Murphyramiritus/planta-nivel-umsa---Public/historico/2022-II/lista de pendientes.docx

VIDEOS:

Isabel: Sensor de temperatura RTD TST487

Sensor de temperatura TC12

Configurar el controlador de temperatura para visualizar los sensores TC y RTD (por realizar)

Configuración PID para el controlador de temperatura (por realizar)

Guido: Manejo del dosificador

Carpeta (Dosificador)

Dosificador Burkert 8035 (por realizar)

Modelo control de temperatura (por realizar)

Roger: SensorUltrasonicoAllenBradley

PrincipioDeFuncionamiento-SensorUltrasonico

Sensor ultrasónico- Allen Bradley modelo 873P-DCAC1S-D5: Características generales – programación – pruebas de laboratorio

Explicación del bloque PID – enfoque continuo (realizado)

Explicación del bloque PID – enfoque Discreto (realizado)

https://drive.google.com/file/d/1aOzCxuXivyHkaeiTq-OtF0UfNlqLcX1q/view?usp=share_link

Controlador PI para el sistema de nivel de líquido (realizado)

https://drive.google.com/file/d/1sBpz8i9ndp3X9Kgfs4qF4b5X31JhYju9/view?usp=share_link

Milton: Motor Bomba y electroválvulas

Funcionamiento del Sistema

Control aplicado al sistema (Por Realizar)

Alvaro: Sensor de presión

Energización (Editar)

Variador de frecuencia (Editar)

Instalación de la máquina virtual (por realizar)

Inducción para el uso de Rslogix y su vinculación al PLC (por realizar)

Diego: Sensor Vibratorio Funcionamiento

Lab_SensVibratorio
