Murphyramiritus/planta-nivel-umsa---Public/historico/2022-II/902/Bitácoras/Bitacora Lab 4_ETN902.docx

Universidad “Mayor de San Andrés”

FACULTAD DE INGENIERIA


CONTROLADOR DEL SISTEMA DE NIVEL DE LIQUIDO

Integrantes: Univ. Espino Marca Mary Isabel

Univ. Condori Mamani Roger

Univ. Linares Poma Guido Alvaro

Carrera: Ing. Electrónica

Materia: ETN 902 / ETN 1034

Docente: Ing. Jorge A. Nava A.

Auxiliares: Univ. Huarachi M. Rhem J.

Univ. Huanca Mita Miguel

Fecha: 13/12/2022

La Paz – Bolivia

Linealización

Se tiene un tanque vertical abierto, provisto de un orificio o restriccion de descarga en su parte inferior, el tanque tiene un area A=l_1 xl_2 , tiene un caudal de entrada q_e por la parte superior , y un caudal q_s a la atmosfera por el orificion mencionado anteriormente.

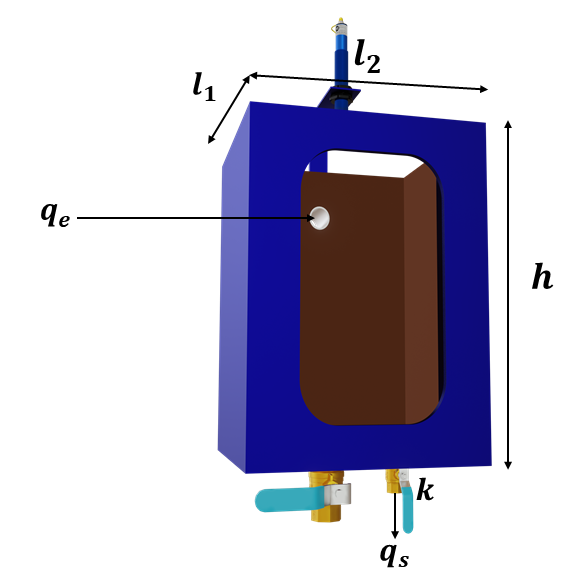
[picture p266: figure]

El caudal que fluye por una una restriccion sigue, basicamente, una ley cuadratica con la presion diferencial, pues se asume regimen turbulento.

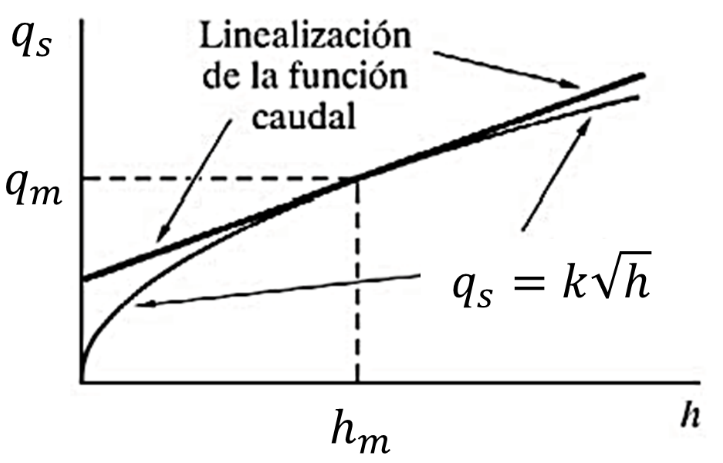
[picture p267: figure]

En nuestro caso , un tanque abierto a la atmosfera, la presion diferencial en la restriccion de salida es debida a la presion hidrostatica existente como consecuencia del nivel de liquido en el tanque.

Si h es la altura del liquido, y k es un coeficiente dependiente de la geometria de la restriccion y de la densidad del liquido, el caudal de salida sera.

q_s =k√h (1)

Balance masico de caudales

entrada-salida=acumulacion

Por otra parte (dV)/(dt) es un caudal, y por otra parte dV=Adh , se tendria:

q_e -q_s =A(dh)/(dt) (2)

Es intuitivo el hecho de que, para un caudal de entrada constante, el nivel se estabilizara en un punto determinado, cuando la salida se iguale con la entrada, ya que a mayor nivel, mayor caudal de salida y viceversa.

Remplazando (2) en (1)

q_e -k√h=A(dh)/(dt) (3)

La ecuacion (3) es una funcion no lineal, entonces para linealizar se escoge un punto de equilibrio, es decir halla la altura de equilibrio h_0 , dado un determinado caudal de entrada q_e .

Entonces q_e =q_s y por tanto h=((q_s)/k)^2 . Pero el calculo se complica para condiciones transitorias , cuando q_s ≠q_e .

Es por ello, que en estos casos se procede linealizar la funcion de la ecuacion (3), mediante alguna forma de ecuacion aproximada, de tal manera que la ecuacion del caudal de salida q_s es sustituida por una ecuacion lineal.

Para ello se define una valor medio de h_m , preferentemente al nivel normal de trabajo, al que llamaremos nivel medio h_m y se opera con una funcion que corresponda a la ecuacion de una recta tangente a la funcion original en el punto [ h=h_m , q_s =q_m ].

Los valores medios, para el nivel medio normalmente el nivel de trabajo seran:

- Pendiente m de la recta tangente

m=(dq_s)/(dh)|_(h=h_m) =1/2k1/(√(h_m)) (4)

- Caudal medio de salida q_m :

q_m =k √(h_m) (5)

Por lo que:

k=(q_m)/(√(h_m)) (6) y, m=(q_m)/(2h_m) (7)

Efectuando un cambio de cordenadas a [ h_m , q_m ], en donde q y h representan los valores absolutos de las variables.

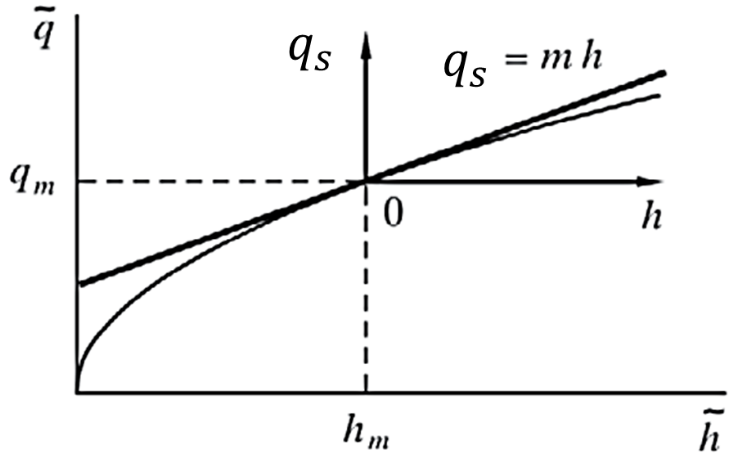
[picture p268: figure]

Con lo que la nueva ecuacion del balance masico queda:

q_e -mh=A(dh)/(dt) (8)

Reordenando y aplicando la transformada de laplace a la ecuacion (8)

Q_e =AsH+mH=H(As+m)

Entonces la función de transferencia será:

H/(Q_e)=1/(As+m)=(1/m)/((As)/m+1)=K/(Ts+1)

H/(Q_e)=K/(Ts+1) (9) funcion de transferencia linealizada

Donde:

K=1/m=Ganancia del sistema

T=A/m=Constante de tiempo

En el laboratorio se obtuvo las siguientes mediciones:

h_m =0.367m

q_m =0.28x10^(-3) (m^3)/s

Realizando calculos y remplazando en (9)

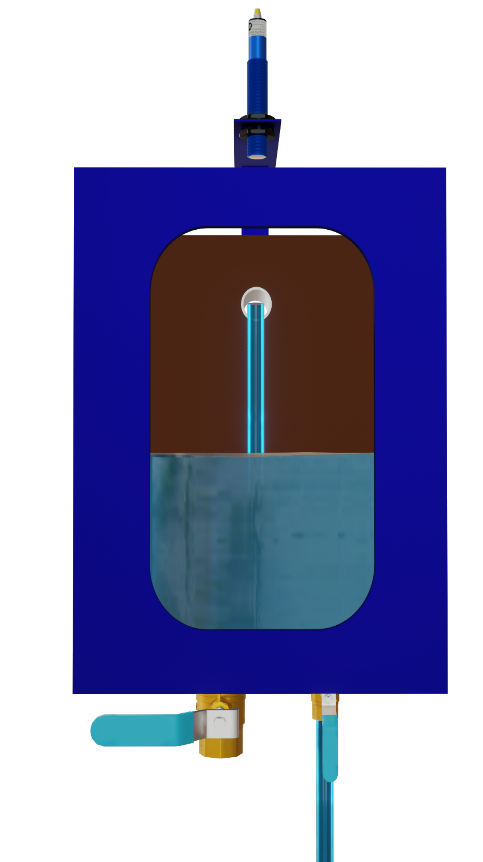
[picture p269: figure]

m=(q_m)/(2h_m)=(0.28x10^(-3))/(2⋅0.367)=0.381x10^(-3) (m^2)/s

H/(Q_e)=1/(As+m)=(1/m)/((As)/m+1)=2624.67/(419.95s+1)

H/(Q_e)=2624.67/(419.95s+1) funcion de transferencia analitica

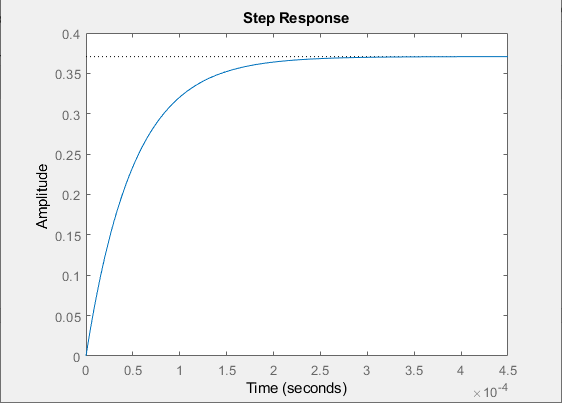
[picture p270: figure]

Por otro lado realizando la linealizacion por series de taylor, tomando la siguiente ecuación no lineal:

A(dh)/(dT)=qe-k_2 a√(2gh)

Realizando la linealizacion se obtiene:

H/(Q_e)=1/(A S+(K_2 a √5)/(√(h_0)))

H/(Q_e)=1/(0.16 S+(0.02√5)/(√0.187))

H/(Q_e)=1/(0.16 S+(0.02√5)/(√0.187))

H/(Q_e)=1/(0.16 S+0.103)

Donde:

A=Area en m^2

h_0 =Altura donde el caudal de salida y entrada es igual,es decir no hay cambio en la altura

a=Areade la valvula de salida (del pequeño)

K_2 =Llave de paso que varia entre 0 y 1, tomando como 1 totalmente abierta

H=Altura de nivel

Q_e =Entrada de caudal

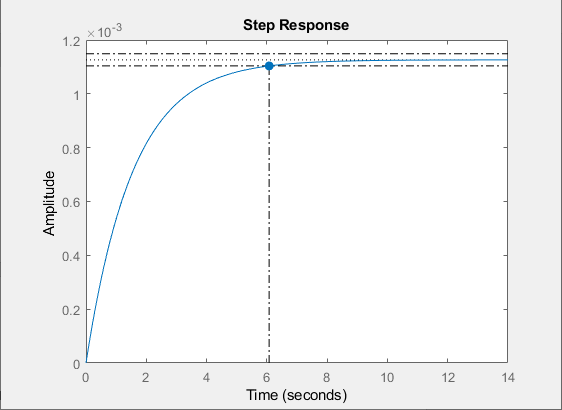
[picture p271: figure]

MODELO DE LA PLANTA

Se tiene un tanque vertical abierto, provisto de un orificio o restricción de descarga en su parte inferior, el tanque tiene un área A=l_1 xl_2 , tiene un caudal de entrada q_e por la parte superior , y un caudal q_s a la atmosfera por el orificio mencionado anteriormente.

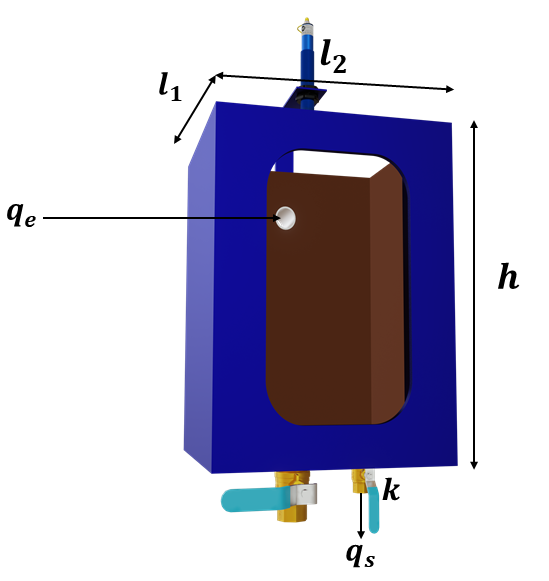
[picture p272: figure]

Donde:

A=l_1 xl_2 : área del tanque

q_e : caudal de entrada

q_s : caudal de salida

k: coeficiente de restricción

h: altura del deposito

Ecuaciones fundamentales

Aplicando la transformada de Laplace

Caudal por la restricción

Caudal en la capacidad del tanque

Reordenando y reemplazando la ecuación (6) y (8) en (3)

Despejando obtenemos la función de transferencia

En el laboratorio se obtuvo las siguientes medidas:

Realizando cálculos y remplazando

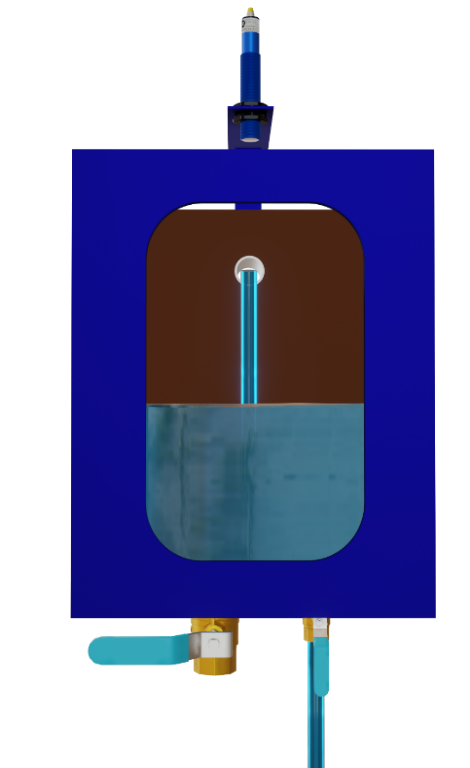
[picture p273: figure]

Vista frontal del tanque superior

Función de transferencia experimental

La FT experimental se obtuvo tomando datos de la altura h cada 20 (s) hasta que logre alcanzar su punto de equilibrio con un caudal de entrada

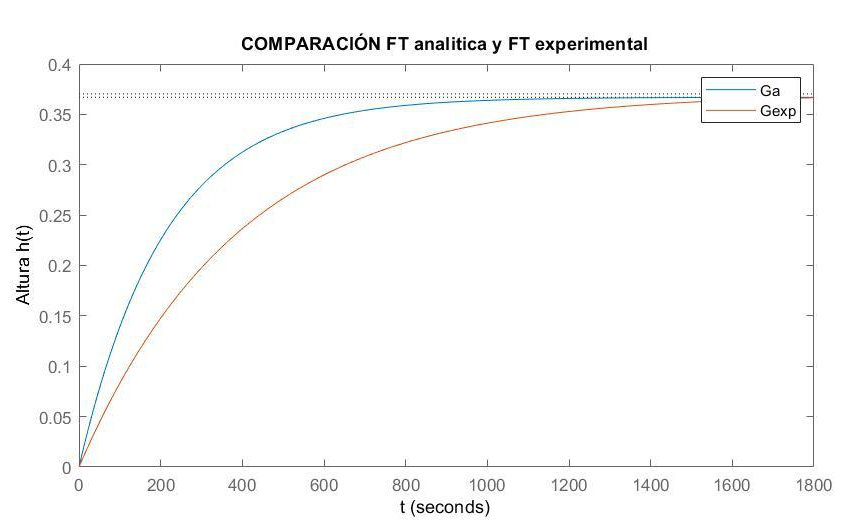
[picture p274: figure]

DIAGRAMA EN BLOQUES

h(t)

h(t)

qe(t)

u(t)

e(t)

ref

CONTROL

ACTUADOR

PLANTA

SENSOR

PID

h(t)

h(t)

qe(t)

u(t)

e(t)

ref

CONTROL

VDF +Bomba

PLANTA

SENSOR

+

- G_(VDF) es la función de transferencia del variador de frecuencia más la bomba

G_(VDF) =(Q_(max))/f

- G_s es la función de transferencia del sensor

G_s =1

Porque la altura que va tomar en el tanque la va a enviar tal cual al comparador

- G_P es la función de transferencia de la planta

H/(Q_e)=1/(0.16 S+0.103)

Elementos a utilizar

- PLC Micro Logix 1100 (Controlador)
- Sensor ultrasónico (sensor en la realimentación)
- Sensor de presión (sensor en la realimentación, opcional)
- Sensores vibratorios (para marcar las limitaciones del tanque)
- Variador de frecuencia y bomba (actuador)

Instrumentos de Medición

- Flujómetro (para medir el caudal de entrada)

Definición de variables

Válvula pequeña siempre abierta (parte del sistema)

Válvula grande como perturbación.

Variable a controlar: El caudal de entrada

Variable Medible: Corriente en función de altura (sensor ultrasónico) que se entrega al PLC

Variable Controlada: Altura del nivel de líquido

Variable manipulada: Frecuencia del VFD

Perturbación: Caudal de Salida válvula grande, agregación de líquido en el tanque superior.

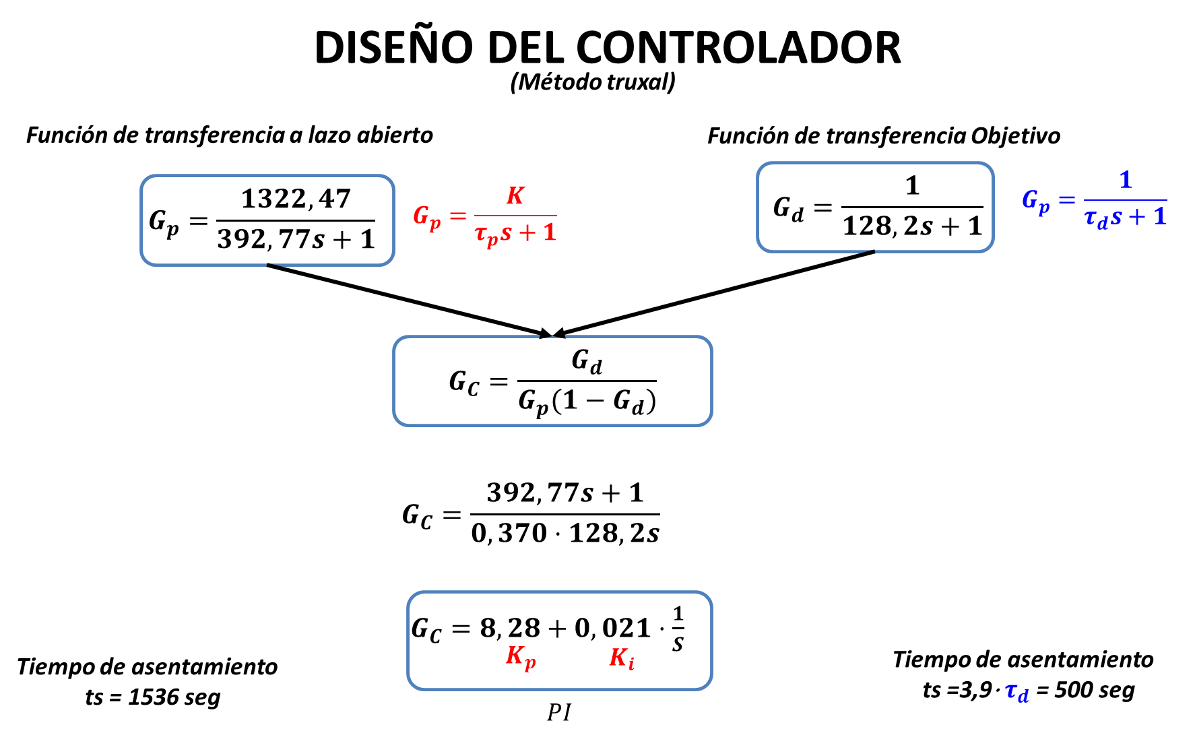
[picture p275: figure]
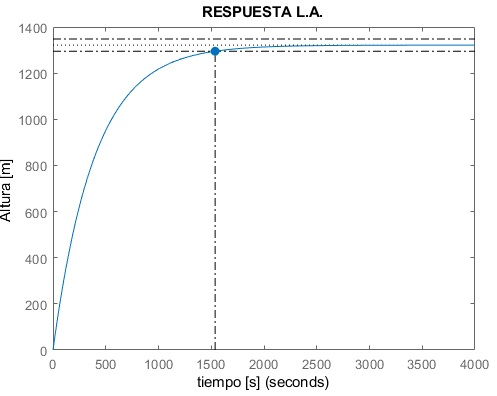
[picture p276: figure]
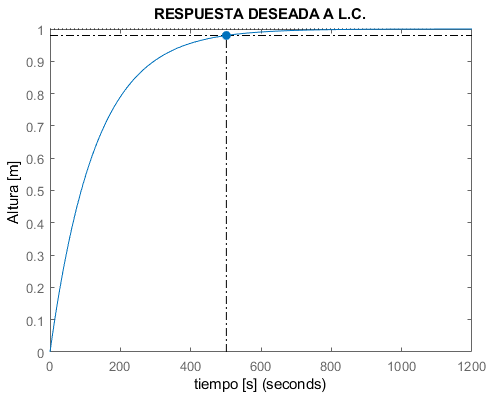
[picture p277: figure]

Diseño del controlador – Función de transferencia a lazo abierto discreto

Se procede a discretizar por el método ‘zoh’ (retenedor de orden cero)

FUNCION DE TRANSFERENCIA DE LA PLANTA

Si consideramos 10 muestras por constante de tiempo

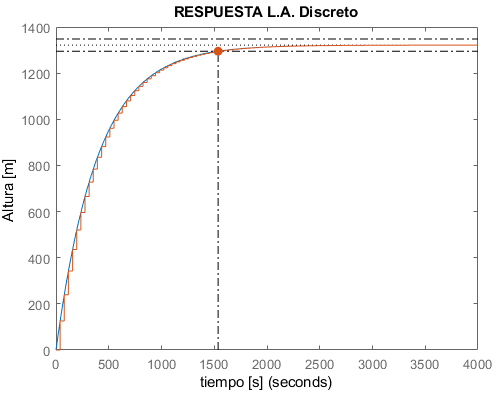
[picture p278: figure]

Periodo de muestreo

realizando la simulación para la perturbación en el sistema

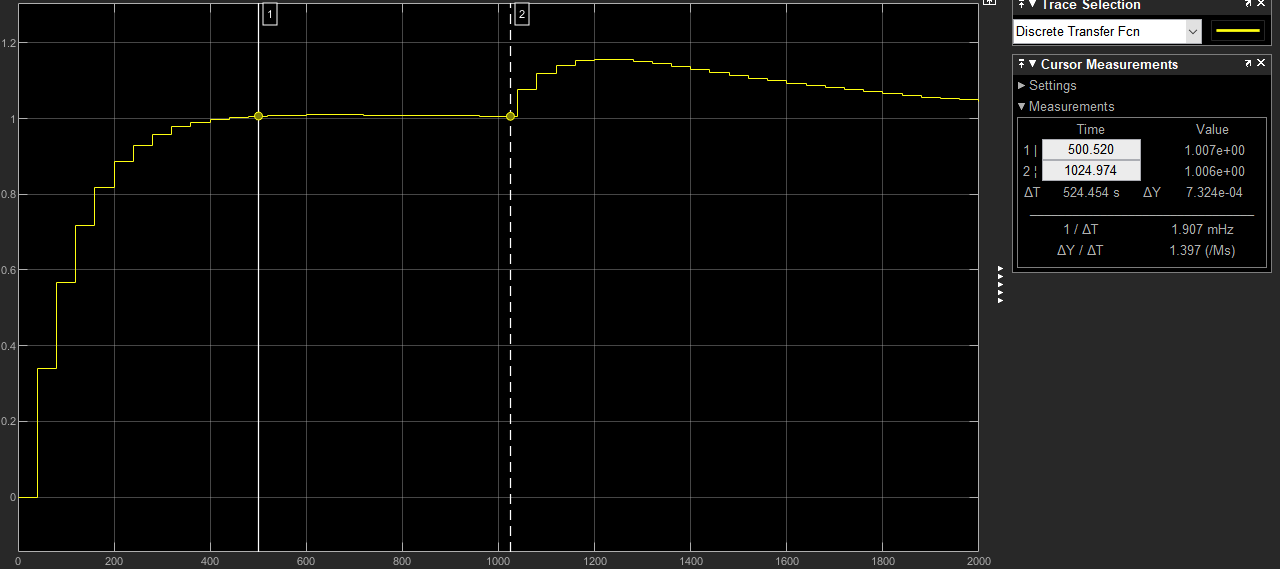
[picture p279: figure]

Respecto al bloque PID y el periodo de muestreo

La instrucción PID y el muestreo de la variable de proceso deben actualizarse periódicamente.

Este tiempo de actualización está relacionado con el proceso físico que se está controlando

Asegurar que la entrada analógica utilizada para la variable de proceso se actualice en el procesador a una velocidad significativamente mayor al tiempo de actualización de la variable de proceso.

Ejemplo: Si el lazo PID está en una tarea periódica de 250 ms, use un tiempo de actualización UDP=0,25 y configure el módulo de entrada analógica para producir datos al menos 25 a 50 ms.

IMPLEMENTACIÓN

El control PID es un sistema comun de lazo cerrado, que se usa para mantener propiedades fisicas como presion, temperatura, longitud, etc. En procesos automatizados.

El PLC micrologix 1100 de la serie B, tiene la instrucción PID que basicamente controla el cricuito a lazo cerrado, al comparar la variable de entrada o proceso de un modulo de entrada analogica con el punto de referencia del sistema.

La diferencia entre el punto de referencia y la variable de proceso se denomina error, y el error se analiza mediante el calculo del PID y proporciona una salida o una variable de control al modulo de salida analogica para cumplir con el punto de referencia definido por los requisitos del sistema.

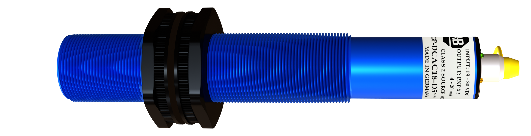
[picture p280: figure]
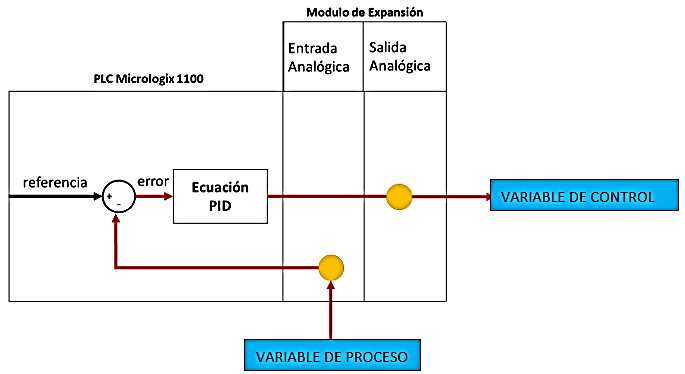
[picture p281: figure]
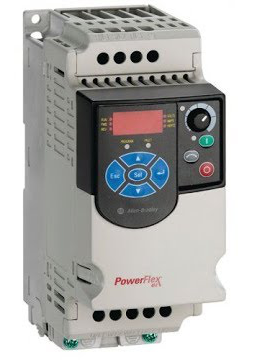
[picture p282: figure]
Ver las imágenes de origen

Sensor ultrasónico

salida de corriente 4-20 mA

Variador de frecuencia

Entrada de corriente 4-20 mA

En primer lugar el control a lazo cerrado, significa que el controlador tiene una retroalimentacion o idea de la reaccion del dispositivo que esta siendo controlado. En este caso se controla un motor bomba a traves del variador de frecuencia, mientras que el controlador usa un sensor para determinar su velocidad.

A continuacion se muestra el diagrama de un controlador PID, donde P significa proporcional, I integral, y D derivativa, juntos representan el controlador.

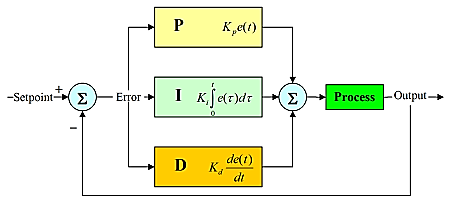
[picture p283: figure]

C_(PID) =Kp[e(t)+K_i ∫ e(t)dt+K_d (de(t))/(dt) ]

Cada una de las tres partes tiene coeficientes constantes Kp, Ki y Kd , estas constantes son los valores de ajuste y representan cuanto depende el control del proceso de PID.

Del manual de referencia del conjunto de instrucciones para el Micrologix 1100, a continuacion se muestra el comando PID.

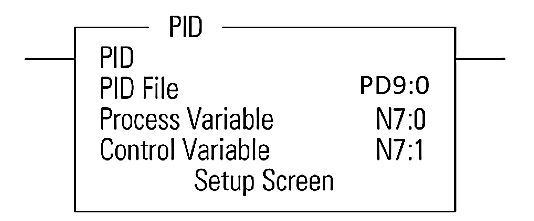
[picture p284: figure]

El comando PID contiene un numero de archivo PD9:X, el cual se la crea de la siguiente manera:

En el programa Rslogix 500, creamos el archivo de datos, en la carpeta Data Files, como se indica:

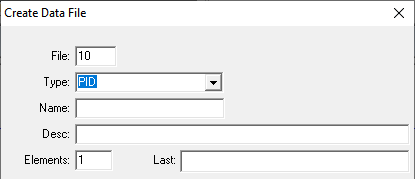
[picture p285: figure]

Se debe definir la variable de proceso y de control, mencionados anteriormente.

Para la configuracion del controlador se debe ingresar en setup screen

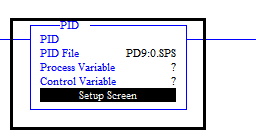
[picture p286: figure]

Desplegandose la siguiente ventana:

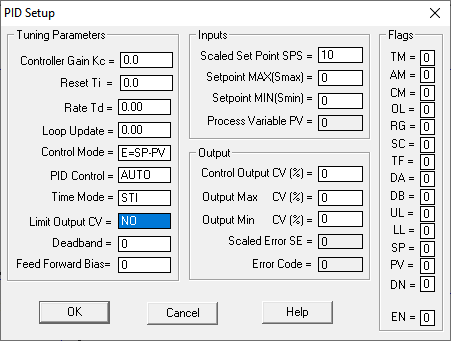
[picture p287: figure]

Dentro de la configuracion, mediante diseño se deben determinar varios parametros como Kc, Ti, Td, Set-point, etc.

Entonces se utilizara el PID para controlar la altura del nivel de liquido de un deposito, usando un transmisor de nivel, como variable de proceso y como variable de control la señal de corriente entregada al variador de frecuencia a una determino nivel de referencia.

Las instrucciones que se utilizaran son las siguientes:

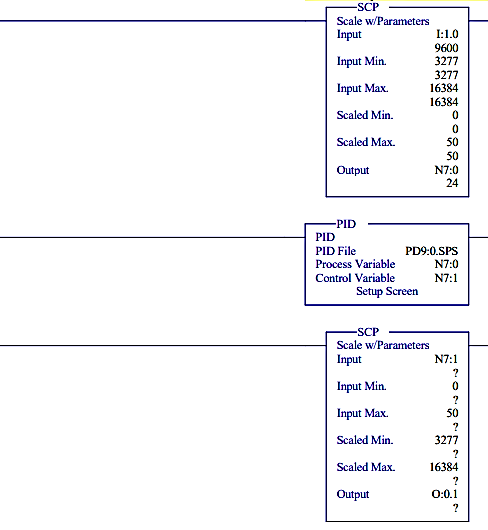
[picture p288: figure]

VARIABLE DEL PROCESO

CONTROL PID

VARIABLE DE CONTROL

Procedimiento SCP para la variable de proceso.

La variable de proceso convierte de 0 a 50 cm, en una senal de 4 a 20 mA, mediante una relacion lineal, es decir el transmisor produce una senal de 4 mA a 0 cm, y a 50 cm produce una senal de 20 mA.

El modulo de entrada analogica convierte la señal de 4 a 20 mA, en un valor digital en el rango de 3277 a 16384, es decir una senal de 4 mA da como resultado un valor de 3277 y una señal de 20 mA da como resultado un valor 16384

Este valor de entrada se almacena en memoria denomina N7:0

Procedimiento SCP para la variable De Control.

La variable de control denominada N7:1 es propia del controlador PID, entonces el rango que varia es de 0 a 50 cm y debe ser escalado al rango de 3277 – 16384.

Con la variable escalada el PLC convierte el valor digital nuevamente en una senal analogica, es decir del valor escalado 3277 a 16384, se convierte nuevamente en una senal de corriente de 4 a 20 mA.

PRUEBAS DEL CONTROLADOR CON PERTURBACION

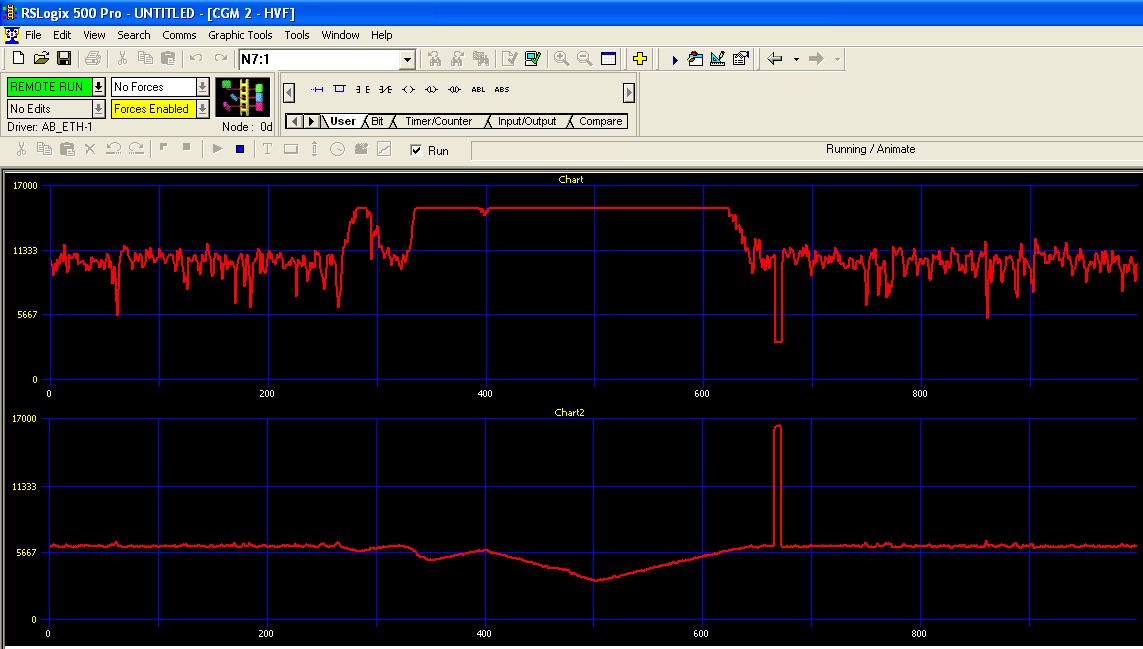
[picture p289: figure]
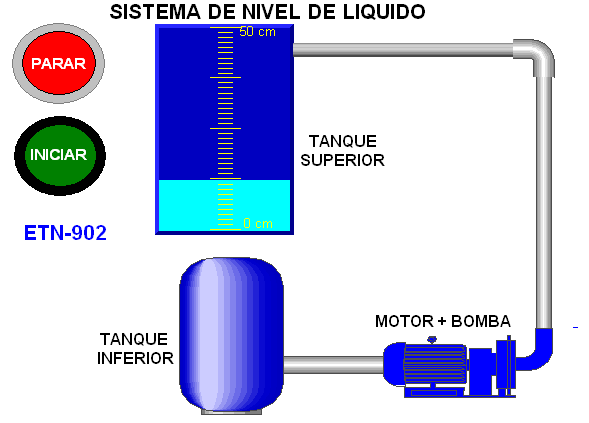
[picture p290: figure]

INTERFAZ GRAFICA PARA HMI COMPACT 600 ALLEN BRADLEY
