Murphyramiritus/planta-nivel-umsa---Public/historico/2023-I/BITACORA 2/Laboratorio2.pptx

## CARACTERIZACIÓN Y DESARROLLO DE LA PLANTA

INTEGRANTES: Arias Llampaso Leidy Melany
Espino Marca Mary Isabel
Laura Mamani Vania Cindy
Ramos Apaza Marco Daniel

## INDICE

- Análisis teórico
- Función de transferencia
- Respuesta temporal del sistema
- Respuesta en frecuencia del sistema
- Estabilidad absoluta
- Análisis en discreto
- Estabilidad en discreto
- Análisis experimental
- Función de transferencia
- Conclusiones

## ANALISIS TEÓRICO

## Nivel de un tanque con restricción de descarga


- El caudal de salida q_s depende de la restricción R.
- La válvula de salida No interviene en el proceso (No influye en la restricción)
- La altura h depende del caudal de entrada q_e .
- El caudal de salida q_s también depende de la altura h.

## Análisis


El caudal de entrada debe ser suficiente para permitir que se tenga un caudal de salida y permita el aumento de nivel

## Análisis


La altura es directamente proporcional al caudal, donde hay un g(t) que relaciona la altura con el caudal.
h(t)=g(t)∗q(t)

## Slide 7

Análisis

q(t)=q_R (t)+q_C (t)
h(t)=g(t)∗q(t)

Reordenando:

L{ }

Q(s)=Q_R (s)+Q_C (s)
H(s)=G(s)∗Q(s)

G(s)=(H(s))/(Q(s))

Función de transferencia

## Slide 8

Análisis

Parámetros constantes:

R=(dh)/(dq)

R es un coeficiente que indicia la relación entre la variación de nivel y la variación de caudal de salida.

C es la relación entre la variación del contenido y la variación del nivel.

C=([cm^3 ])/(cm)=A

## Slide 9

Análisis

Caudal por la restricción:

Considerando que no hay acumulación

A mayor altura, mayor caudal.

h(t)=q_r (t)∗R

H(s)=Q_R (s)∗R

L{ }

Q_R (s)=1/RH(s)

Caudal en la capacidad del tanque:

Considerando que hay acumulación

h(t)∗C=∫ q_c (t)dt

h(t)=1/c∫ q_c (t)dt

El volumen acumulado es la suma de todo el caudal que se a acumulado en un tiempo.

L{ }

H(s)=1/(Cs)Q_c (s)

Q_C (s)=1/RH(s)

## Slide 10

Análisis

EL caudal que entra al tanque es igual al caudal que sale mas el caudal que se queda

Q(s)=Q_R (s)+Q_C (s)

Q_C (s)=Cs∗H(s)

Q_R (s)=1/RH(s)

Q_C (s)=(1/R+Cs)∗H(s)
Q(s)=((1+RCs)/R)∗H(s)

G(s)=R/(1+τs)

Q(s)=1/RH(s)+Cs∗H(s)

(H(s))/(Q(s))=R/(1+RCs)→G(s)=R/(1+RCs)→

## Datos

Reemplazando:
Capacitancia Restricción

C=39,8 x 39,8 [cm^2 ]

C=1584[cm^2 ]

R=h/(q_s)=(25[cm])/(259.62[(cm^3)/s])

R=0.09629[s/(cm^2)]

Función de transferencia

(H(s))/(Q(s))=(0,09629)/(152,5s+1)

## Nivel de un tanque con restricción de descarga

Retardo de primer orden

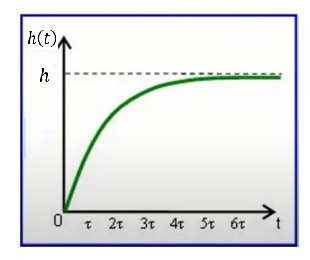
[picture p329: figure]

G(s)=(0,09629)/(152,5s+1)

G(s)=(0,09629)/(152,5s+1)

## Nivel de un tanque con restricción de descarga

Retardo de primer orden

Y(s)= k/(τs+1)U(s)

y(t)=k(∆u)[1−e^((−t/τ)) ]

y(t)=2,495[1−e^((−t/158)) ]

## RESPUESTA TEMPORAL DEL SISTEMA

## Slide 15

Respuesta temporal del sistema:

F(s)=(Y(s))/(U(s))=(b0)/(s+a0)=K/(τs+1)
Donde: el sistema tiene un polo en: −a0
k: es la ganancia de estado estacionario, la cual entrega el valor que toma la respuesta del sistema para un tiempo que tiende a infinito.
k=(b0)/(a0)
La constante τ , es la constante de tiempo, la cual indicara el tiempo en el cual el sistema tiene un 63,21% del valor en estado estacionario.
τ=1/(a0)

## Slide 16

Análisis de la respuesta a un escalón:
U(s)=A/s ; y(s)=K/(τs+1)∗25/s=K∗(a/(τs+1)+b/s)=K∗(A/(τs+1)+b/s)
A=−τ ;B=1
y(s)=K∗((−τ)/(τs+1)+1/s)=K∗((−1)/(s+1/τ)+1/s)

y(t)=A∗K∗(1−e^((−t)/τ) );t≥0

## Slide 17

Análisis de la respuesta a un escalón:

y(t)=A∗K∗(1−e^((−t)/τ) );t≥0

t | y(t)
0 | 0
τ | AK(1−e^(−1) )=0,632AK
2τ | AK(1−e^(−2) )=0,865AK
3τ | AK(1−e^(−3) )=0,95AK
4τ | AK(1−e^(−4) )=0,982AK
∞ | AK(1−e^(−∞) )=AK

Teorema del valor final:
y_(∞) =lims→0s∗E(s)
y_(∞) = s∗1/s∗(0,09629)/(152,5s+1)


y_(∞) =0.09629∗A

## RESPUESTA EN FRECUENCIA DEL SISTEMA

## Respuesta en frecuencia

Describe la respuesta en estado estacionario de un sistema a las entradas sinusoidales de frecuencias variables

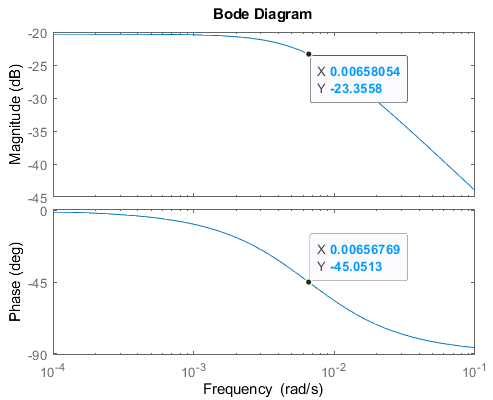
[picture p330: figure]

Función de transferencia:

G(s)=0.09629/((152.5∗s+1))

s=−1/(152,5)

SISTEMA ESTABLE

## Slide 20

ANALISIS TEORICO

Margen de la ganancia: ‖Gp‖=k
0.09629/((152.5∗s+1))=k
K=0.09629

M argen de fase: <Gp=<0.09629/((152.5∗s+1))
<0.09629/((152.5∗jw+1))
θ_p =tan^(−1) (0/0.09629)−tan^(−1) ((152.5∗w)/1)

En decibelios:
dB =20logk
dB =20log0.09629

dB=-20,32

;con ω=6.56∗10^(−3)

θ_p =−45°

## ESTABILIDAD ABSOLUTA

## Estabilidad absoluta

El polo se encuentra en el lado izquierdo, próximo a el origen de coordenadas, lo que indica una respuesta lenta y se encuentra estable.

G(s)=0.09629/((152.5∗s+1))

Análisis de estabilidad según Routh Hurwitz
Se cumple la condición necesaria, todos los coeficientes del polinomio característico son positivos, además es un polinomio ordenado y completo.


S=0,006557

## ANALISIS EN DISCRETO

## Análisis en Discreta

Elección de periodo de muestreo:
Según el criterio de muestreo de Nyquist-Shannon ,el periodo de muestreo mínimo:
T_S <(2∗π)/(ω_C)→ω_C =1/τ
ω_C →La frecuencia de corte
T_S →El periodo de muestreo
- La frecuencia de corte es el punto en el cual la magnitud de la función de transferencia se reduce en 3 dB respecto a su valor de baja frecuencia.
- La condición garantiza que se muestree la señal lo suficientemente rápido como para evitar el efecto de aliasing.
(H(s))/(Q_i (s))=0.09629/(152.5∗s+1)
(H(s))/(Q_i (s))=0.0006314/(s+0,006557)
Transformada Z según tablas :

w_c =1/152.5=0,006557

T_s <(2∗π)/(w_c)<(2∗π)/(0,006557)
T_s =958,24

G(z)=(0.0006314∗Z)/(Z−e^(−0,006557∗T))

## Análisis en Discreta

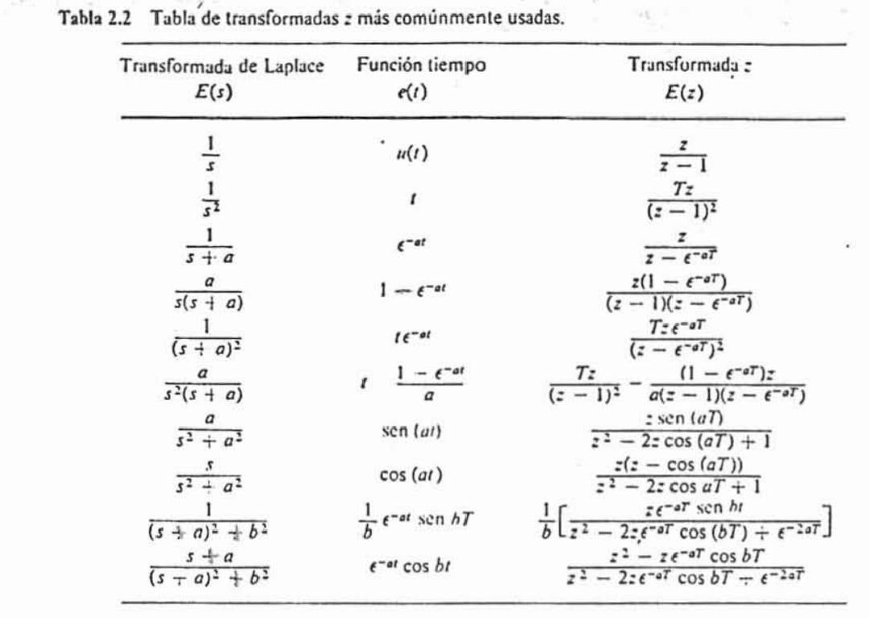
[picture p331: figure]

## Análisis en Discreta

- Criterio del tiempo de respuesta : T_s =τ/10=152.5/10=15.25

G(z)=(0.0006314∗Z)/(Z−e^(−0,006557∗T))

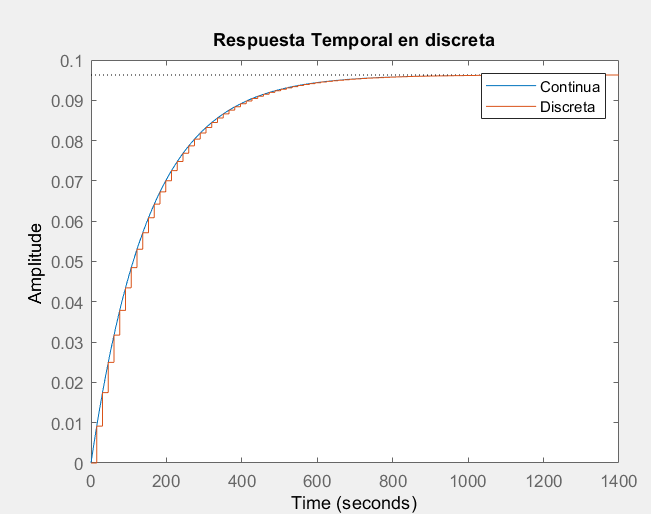
[picture p332: figure]

G(z)=(0.0006314∗Z)/(Z−e^(−0,09999))

G(z)=(0.0006314∗Z)/(Z−0,9048)

## ESTABILIDAD EN DISCRETO

## Estabilidad en discreta

e_(∞) =limz→1(1−z^(−1) )∗U(z)∗1/(1+G(z))

G(z)=(0.0006314∗Z)/(Z−0,9048)

El sistema es estable, debido que se encuentra dentro del circulo de radio unidad, según
e^(sT) =Z

- Error en estado estacionario:

e_(∞) =limz→1(1−z^(−1) )∗U(z)∗1/(1+(0.0006314∗Z)/(Z−e^(−0,09999)))

e_(∞) =limz→1((z−1)/z)∗z/(z−1)∗(Z−e^(−0,09999))/(Z−e^(−0,09999) +0.0006314∗Z)

Entrada escalón:

U(z)=z/(z−1) ;

G(z)=(0.0006314∗Z)/(Z−e^(−0,09999))

e_(∞) =limz→1(Z−e^(−0,09999))/(1.0006314∗Z−e^(−0,09999))

e_(∞) =(1−e^(−0,09999))/(1.0006314−e^(−0,09999))

e_(∞) =0.9934

## ANALISIS EXPERIMENTAL

## Slide 30

Función de transferencia experimental

Para la implementación de datos, se realizo la medición de nivel de flujo en el tiempo para un caudal de entrada constante (el mismo caudal que utilizamos para obtener la función de transferencia teórica).
La medición de nivel de liquido se realizo cada 10 segundos para obtener resultados óptimos.

## Slide 31

Función de transferencia experimental

Entonces con los siguientes datos:
- Caudal de entrada: Q_e =261[(cm^3)/s]
- Tiempo de medición: t=10 s
Con ello, empezamos a tomar nota de los datos en una tabla Excel.
Se hizo la acumulación de 256 muestras en aproximadamente 43 min.

## Slide 32

El la tabla se muestra la respuesta temporal:


## Slide 33

- Con la tabla de datos y con la función “ident” en Matlab, es posible obtener la función de transferencia:
- Definiremos como entrada al caudal y como salida la altura.

## Slide 34


Función de transferencia experimental


(H(s))/(Q(s))=(0,09569)/(303s+1)


## RESPUESTA TEMPORAL DEL SISTEMA (EXPERIMENTAL)

## Slide 36

Análisis de la respuesta a un escalón:
U(s)=A/s ; y(s)=K/(τs+1)∗25/s=K∗(a/(τs+1)+b/s)=K∗(A/(τs+1)+b/s)
A=−τ ;B=1
y(s)=K∗((−τ)/(τs+1)+1/s)=K∗((−1)/(s+1/τ)+1/s)

y(t)=A∗K∗(1−e^((−t)/τ) );t≥0

## Slide 37

Análisis de la respuesta a un escalón:

y(t)=A∗K∗(1−e^((−t)/τ) );t≥0

t | y(t)
0 | 0
τ | AK(1−e^(−1) )=0,632AK
2τ | AK(1−e^(−2) )=0,865AK
3τ | AK(1−e^(−3) )=0,95AK
4τ | AK(1−e^(−4) )=0,982AK
∞ | AK(1−e^(−∞) )=AK

Teorema del valor final
y_(∞) =lims→0s∗E(s)
y_(∞) = s∗A/s∗(0,09569)/(303s+1)


y_(∞) =0.09569∗A

## Slide 38

Respuesta temporal


## RESPUESTA EN FRECUENCIA DEL SISTEMA (EXPERIMENTAL)

## Respuesta en frecuencia

Describe la respuesta en estado estacionario de un sistema a las entradas sinusoidales de frecuencias variables


Función de transferencia:

G(s)=0.09569/((303∗s+1))

s=−1/303

SISTEMA ESTABLE

## Slide 41

ANALISIS TEORICO

Margen de la ganancia: ‖Gp‖=k
0.09569/((303∗s+1))=k
K=0.09569

M argen de fase: <Gp=<0.09569/((303∗s+1))
<0.09569/((303∗jw+1))
θ_p =tan^(−1) (0/0.09569)−tan^(−1) ((303∗w)/1)

En decibelios:
dB =20logk
dB =20log0.09569

dB=-20,3827

;con ω=3,3∗10^(−3)

θ_p =−45°

## ESTABILIDAD ABSOLUTA

## Estabilidad absoluta

El polo se encuentra en el lado izquierdo, próximo a el origen de coordenadas, lo que indica una respuesta lenta y se encuentra estable.

G(s)=0.09569/((303∗s+1))

Análisis de estabilidad según Routh Hurwitz
Se cumple la condición necesaria, todos los coeficientes del polinomio característico son positivos, además es un polinomio ordenado y completo.

S=0,0033

## ANALISIS EN DISCRETO

## Análisis en Discreta

Elección de periodo de muestreo:
Según el criterio de muestreo de Nyquist-Shannon ,el periodo de muestreo mínimo:
T_S <(2∗π)/(ω_C)→ω_C =1/τ
ω_C →La frecuencia de corte
T_S →El periodo de muestreo
- La frecuencia de corte es el punto en el cual la magnitud de la función de transferencia se reduce en 3 dB respecto a su valor de baja frecuencia.
- La condición garantiza que se muestree la señal lo suficientemente rápido como para evitar el efecto de aliasing.
(H(s))/(Q_i (s))=0.09629/(152.5∗s+1)
(H(s))/(Q_i (s))=0.0006314/(s+0,006557)
Transformada Z según tablas :

w_c =1/152.5=0,006557

T_s <(2∗π)/(w_c)<(2∗π)/(0,006557)
T_s =958,24

G(z)=(0.0006314∗Z)/(Z−e^(−0,006557∗T))

## Análisis en Discreta

## Análisis en Discreta

- Criterio del tiempo de respuesta : T_s =τ/10=152.5/10=15.25

G(z)=(0.0006314∗Z)/(Z−e^(−0,006557∗T))

G(z)=(0.0006314∗Z)/(Z−e^(−0,09999))

G(z)=(0.0006314∗Z)/(Z−0,9048)

## ESTABILIDAD EN DISCRETO

## Estabilidad en discreta

e_(∞) =limz→1(1−z^(−1) )∗U(z)∗1/(1+G(z))

G(z)=(0.0006314∗Z)/(Z−0,9048)

El sistema es estable, debido que se encuentra dentro del circulo de radio unidad, según
e^(sT) =Z

- Error en estado estacionario:

e_(∞) =limz→1(1−z^(−1) )∗U(z)∗1/(1+(0.0006314∗Z)/(Z−e^(−0,09999)))

e_(∞) =limz→1((z−1)/z)∗z/(z−1)∗(Z−e^(−0,09999))/(Z−e^(−0,09999) +0.0006314∗Z)

Entrada escalón:

U(z)=z/(z−1) ;

G(z)=(0.0006314∗Z)/(Z−e^(−0,09999))

e_(∞) =limz→1(Z−e^(−0,09999))/(1.0006314∗Z−e^(−0,09999))

e_(∞) =(1−e^(−0,09999))/(1.0006314−e^(−0,09999))

e_(∞) =0.9934

## GRAFICA EN RESPUESTA PASO


## CONCLUSIONES

- Se pudo obtener la función de transferencia experimental y teórica, dándonos la misma altura de referencia.
- Pero se pudo evidenciar que hay una diferencia en el tiempo de subida en ambas funciones, esto es debido a que no estamos considerando las turbulencias que se presentan al momento de cargar el liquido en el tanque.
- La respuesta temporal de la planta teórica es equivalente a la respuesta experimental obtenida, sin embargo la influencia de las perturbaciones modifican la respuesta transitoria.
- El sistema nivel de liquido presenta una respuesta temporal lenta, para lo cual fueron necesarios muestras relativamente grandes T= 20[s] , pero para mayor precisión se tomaron varias mediciones(T= 10[s] ) para su obtención.
