Murphyramiritus/planta-nivel-umsa---Public/historico/2023-I/BITACORA 3/ETN-1034_BITACORA_3.docx

Universidad “Mayor de San Andrés”

FACULTAD DE INGENIERIA


LABORATORIO 1

CONTROLADOR DEL SISTEMA DE NIVEL DE LIQUIDO

Integrantes: Univ. Arias Llampaso Leidy Melany

Univ. Espino Marca Mary Isabel

Univ.Laura Mamani Vania Cindy

Univ. Ramos Apaza Marco Daniel

Carrera: Ing. Electrónica

Materia: Aplicación de Técnicas de Control ETN 1034

Docente: Jorge A. Nava A.

Fecha: 1/05/2023

La Paz – Bolivia

# 1. OBJETIVOS:

- Diseñar un controlador en el espacio de estados para el sistema de control de nivel.

# 2. TEORIA:

## 2.1. Métodos para diseñar un controlador en el espacio de estados:

Existen varios métodos para diseñar un controlador en el espacio de estado para un sistema de control. Estos métodos incluyen:

1. Colocación de polos: este método consiste en colocar los polos de circuito cerrado del sistema en las ubicaciones deseadas para lograr el rendimiento deseado. El método de colocación de polos se puede realizar utilizando diferentes técnicas, como la fórmula de Ackermann, la colocación de valores propios y el regulador cuadrático lineal (LQR).
2. Regulador cuadrático lineal (LQR): este método implica minimizar una función de costo cuadrático que representa el rendimiento del sistema y el esfuerzo de control. El método LQR se puede utilizar tanto para sistemas de entrada única y salida única (SISO) como de entrada múltiple y salida múltiple (MIMO).
3. Control óptimo: este método implica encontrar la entrada de control que minimiza una función de costo que representa el rendimiento del sistema y el esfuerzo de control. El método de control óptimo se puede utilizar tanto para sistemas lineales como no lineales.
4. Control infinito H: este método implica diseñar un controlador que minimice el rendimiento del sistema en el peor de los casos sujeto a ciertas restricciones. El método de control H-infinity se puede utilizar para sistemas SISO y MIMO.

## 2.2. Método colocación de polos:

- Con la fórmula de Ackerman:

Un método utilizado para transformar un controlador de espacio de estado en una matriz de ganancia de retroalimentación para un sistema lineal. La fórmula está dada por:

K=[1]*C_o^(-1) *ϕ(A)

Donde:

K: es la matriz de ganancia de retroalimentación,

A: es la matriz de estado

B: es la matriz de entrada,

C_o^(-1) : es la matriz inversa de controlabilidad del sistema

ϕ(A): es la matriz resultante de la evaluación de la matriz a en el polinomio deseado.

Para usar la fórmula de Ackerman para diseñar un controlador de espacio de estado, se pueden seguir los siguientes pasos:

- Determine las ubicaciones deseadas de los polos de bucle cerrado: El primer paso es determinar las ubicaciones deseadas de los polos de bucle cerrado en función de los requisitos del sistema.
- Calcule la matriz de ganancia de retroalimentación: una vez que se determinan las ubicaciones deseadas de los polos de bucle cerrado, la matriz de ganancia de retroalimentación se puede calcular utilizando la fórmula de Ackerman.
- Implementar el controlador: luego de calcular la matriz de ganancia de retroalimentación, se puede implementar utilizando diferentes herramientas de hardware y software, según los requisitos específicos del sistema.
- Probar y ajustar el controlador: finalmente, el controlador debe probarse y ajustarse para garantizar que cumpla con los requisitos del sistema. Esto se puede hacer realizando experimentos y ajustando los parámetros del controlador según sea necesario.

Es importante tener en cuenta que la fórmula de Ackerman asume que el sistema es completamente controlable, lo que significa que es posible conducir el sistema desde cualquier estado inicial a cualquier estado final en un tiempo finito utilizando una entrada de control. Si el sistema no es completamente controlable, es posible que la fórmula de Ackerman no sea aplicable.

## 2.3. La controlabilidad y la observabilidad:

### 2.3.1. Controlabilidad:

- La controlabilidad es la propiedad que indica si el comportamiento de un sistema puede ser controlado por sus entradas.
- Se dice que un sistema es completamente controlable si puede pasar de cualquier estado inicial a cualquier estado final en un tiempo finito usando una entrada de control.
- La controlabilidad depende de la arquitectura interna del sistema y los valores de sus componentes.

### 2.3.2. Observabilidad:

- La observabilidad es la propiedad que indica si el comportamiento de un sistema se puede observar a partir de sus salidas.
- Se dice que un sistema es completamente observable si sus estados internos pueden determinarse a partir de sus salidas.
- La observabilidad depende de la arquitectura interna del sistema y los valores de sus componentes.

# 3.PROCEDIMIENTO.

Para diseñar un controlador de espacio de estado para un sistema de control de nivel, se pueden seguir los siguientes pasos:

- Obtener la representación del espacio de estados del sistema: El primer paso es obtener la representación del espacio de estados del sistema de control de nivel. Esto se puede hacer modelando el sistema usando ecuaciones diferenciales y luego transformándolas en forma de espacio de estado.
- Diseñar el controlador de retroalimentación de estado: Una vez que se obtiene la representación del espacio de estado del sistema, el siguiente paso es diseñar el controlador de retroalimentación de estado. Esto se puede hacer utilizando diferentes métodos, como la colocación de polos, el regulador cuadrático lineal (LQR) o el control óptimo.
- Implementar el controlador: después de diseñar el controlador de retroalimentación de estado, se puede implementar utilizando diferentes herramientas de hardware y software, según los requisitos específicos del sistema.
- Probar y ajustar el controlador: finalmente, el controlador debe probarse y ajustarse para garantizar que cumpla con los requisitos del sistema. Esto se puede hacer realizando experimentos y ajustando los parámetros del controlador según sea necesario.

## 2.4. DISEÑO:

A partir de la función de transferencia experimental

(H(s))/(Q(s))=(0,09569)/(303,030*s+1)

Según la respuesta temporal de la planta:

Simulando el comportamiento del sistema para un caudal de entrada de 261,1 cc/seg, tenemos:}


Tiempo de asentamiento:

19,83 min

## 2.5. REQUERIMIENTOS

- El diseño de un controlador por realimentación de estados, tiene los siguientes requerimientos:
- El sistema tenga un tiempo de establecimiento de 4 min
- Un máximo sobrepaso menor al 1%

## 2.6. DISEÑO DEL CONTROLADOR PARA UN SERVOSISTEMA

Esquema de un servosistema de tipo 1 para una planta sin integrador:


### 2.6.1. POLINOMIO CARACTERISTICO DESEADO:

Analizamos los requerimientos:

300=t_s ≥4/(ζω_n); 0.001=Mp≥e^((-ζπ)/(√(1-ζ^2))) ;

Procedimiento:

In(0.001)=(-ζπ)/(√(1-ζ^2)) → (1-ζ^2 )In(0.001)^2 =(ζπ)^2 → ζ=√((In(0.001)^2)/(In(0.001)^2 +π^2))=0.91

ω_n =4/(300*ζ) → ω_n =14.65∙10^(-3)

Sea el polinomio característico de un sistema de 2do orden:

s^2 +2ζω_n s+ω_n ^2 → s^2 +0.0267s+0.2146∙10^(-3)

Las raíces que deseamos serán:

s_(1,2) =-0.01335±6.0314∙10^(-3)

Donde podemos definir las siguientes ecuaciones:

(H(s))/(Q_i (s))=R/(sCR+1) → (H(s))/(Q_i (s))=0.09569/(303*s+1)

Con las ecuaciones:

x(t)=Ax(t)+Bq_i (t)y(t)=Cx(t) → A=[(-1)/303], B=[1/3166.47], C=[1]

x(t)=Ax(t)+Bu(t)y(t)=Cx(t)u(t)=k_1 ξ(t)-Kx(t)ξ(t)=r(t)-y(t)

Entonces tendríamos una representación en espacio de estados de la siguiente manera:

[x(t)ξ(t)]=[A, 0-C, 0][x(t)ξ(t)]+[B0]u(t)+[01]r(t) → x_a (t)=Ax_a (t)+Bu(t)+Er(t)u(t)=-Kx_a (t)

Donde:

A=[(-1)/(RC), 0-1, 0], B=[1/C0] y K=[K -k_1 ]

A=[-3.3003∙10^(-3) , 0-1, 0], B=[31.58∙10^(-3) 0] y K=[K -k_1 ]

Verificamos la controlabilidad del sistema

Co=[B, AB] → Co=[0.625∙10^(-3) 0, -3.8989∙10^(-3) *0.625∙10^(-3) -0.625∙10^(-3) ]

Co=[0.625∙10^(-3) 0, -2.4368∙10^(-6) -0.625∙10^(-3) ] ∴es controlable

Debido a que el error en estado estacionario es lo suficientemente bajo, no es necesario agregar un estado para mejorar la respuesta en régimen permanente.

Por ello se recurrirá a realimentación de estados para matrices de dimensión 1x1 con el método asignación de polos con la fórmula de Ackerman.

DISEÑO DEL CONTROLADOR EN EL ESPACIO DE ESTADOS CON UNA MATRIZ 1X1

Realizamos el siguiente análisis, partimos de la representación externa:

(H(s))/(Q(s))=R/(1+RCs)

si: x_1 =h(t)

→ x_1 = h(t)

x_1 =1/C*q_i (t)-1/(RC)*x_1

→ A=[(-1)/(RC)], B=[1/C], C=[1]

## 2.7. DISEÑO DEL CONTROLADOR EN TIEMPO CONTINUO

Trabajando con el sistema de primer orden

(H(s))/(Q_i (s))=R/(sCR+1) → (H(s))/(Q_i (s))=0.09569/(303*s+1)

Tomando las ecuaciones diferenciales ordinarias que modelan el sistema (1 y 2).

x(t)=Ax(t)+Bq_i (t)y(t)=Cx(t) → A=[(-1)/303], B=[1/3166.47], C=[1]

Analizamos el requerimiento (ts = 4 min = 240 seg):

240=t_s ≥4τ ; τ=60

Sea el polinomio característico de un sistema deseado:

s+1/τ → s+16.6667∙10^(-3)

La raíz que deseamos será:

s=-16.6667∙10^(-3) →ϕ(A)= [(-1)/303]^2 +0.0267*[(-1)/303]+0.2146∙10^(-3) *[1]

ϕ(A)=1.3737*10^(-4)

Calculamos las matrices de ganancia para la realimentación por el método de Ackerman:

K=[1]*C_o^(-1) *ϕ(A)

K=[1]*[1/3166.47]^(-1) *[(-1)/303+16.6667∙10^(-3) ]

K=1*3166.5*13.367∙10^(-3)

K=42,3350

Calculamos la matriz de recompensación para el seguimiento a referencia:

G(s)=C*(sI-(A-BK))^(-1) *B → G(s)=(315,80∙10^(-6))/(s+16.6667∙10^(-3))

Si: s→0 entonces: 1/N=18,9442.4999∙10^(-3) → N=52.6667

## 2.8. DISEÑO DEL CONTROLADOR EN TIEMPO CONTINUO(Experimental)

Trabajando con el sistema de primer orden

(H(s))/(Q_i (s))=R/(sCR+1) → (H(s))/(Q_i (s))=0.09569/(303*s+1)

Tomando las ecuaciones diferenciales ordinarias que modelan el sistema (1 y 2).

x(t)=Ax(t)+Bq_i (t)y(t)=Cx(t) → A=[(-1)/303], B=[1/3166.47], C=[1]

Analizamos el requerimiento (ts = 4 min = 240 seg):

240=t_s ≥4τ ; τ=60

Sea el polinomio característico de un sistema deseado:

→ s^2 +0.0267s+0.2146∙10^(-3)

→ϕ(A)= [(-1)/303]^2 +0.0267*[(-1)/303]+0.2146∙10^(-3) *[1]

ϕ(A)=1.3737*10^(-4)

Calculamos las matrices de ganancia para la realimentación por el método de Ackerman:

K=[1]*C_o^(-1) *ϕ(A)

K=[1]*[1/3166.47]^(-1) *[(-1)/303+16.6667∙10^(-3) ]

K=1*3166.5*13.367∙10^(-3)

K=42,3350

Calculamos la matriz de recompensación para el seguimiento a referencia:

G(s)=C*(sI-(A-BK))^(-1) *B → G(s)=(315,80∙10^(-6))/(s+16.6667∙10^(-3))

Si: s→0 entonces: 1/N=18,9442.4999∙10^(-3) → N=52.6667

## 2.9. DISEÑO DEL CONTROLADOR EN TIEMPO CONTINUO(TEORICO)

Trabajando con el sistema de primer orden

(H(s))/(Q_i (s))=R/(sCR+1) → (H(s))/(Q_i (s))=0.09629/(152,5*s+1)

Tomando las ecuaciones diferenciales ordinarias que modelan el sistema (1 y 2).

x(t)=Ax(t)+Bq_i (t)y(t)=Cx(t) → A=[(-1)/(152,5)], B=[1/(1583,75)], C=[1]

Analizamos el requerimiento (ts = 4 min = 240 seg):

240=t_s ≥4τ ; τ=60

Sea el polinomio característico de un sistema deseado:

Sea el polinomio característico de un sistema deseado:

s+1/τ → s+16.6667∙10^(-3)

La raíz que deseamos será:

s=-16.6667∙10^(-3)

Calculamos las matrices de ganancia para la realimentación por el método de Ackerman:

K=[1]*C_o^(-1) *ϕ(A)

K=[1]*[1/(1583,75)]^(-1) *[(-1)/(152,5)+16.6667∙10^(-3) ]

K=1*3166.5*1.3737*10^(-4)

K=16.02

Calculamos la matriz de recompensación para el seguimiento a referencia:

G(s)=C*(sI-(A-BK))^(-1) *B → G(s)=(6.314*10^(-4))/(s+16.6667∙10^(-3))

Si: s→0 entonces: 1/N=37.8770∙10^(-3) → N=26.4012

Verificando los valores obtenidos

- Una vez obtenido los valores de N=20.42 y k=26.67:
- El sistema tenga un tiempo de establecimiento de 4 min
- Un máximo sobrepaso menor al 1%
- Si bien la simulación en matlab es buena, al introducir los valores de N y K al PLC, esta manda una señal de “fault”
- El Sistema no functional
- Modificando el tiempo de establecimiento de 8 min
- Obtenemos los valores de N=13.183 y k=2.733:
- La simulación en Matlab es buena, al introducir los nuevos valores de N y K al PLC, este ya no manda una señal de “fault”
- El sistema funciona.


## 2.10. Programación en PLC


## 2.11. CONCLUSIONES

Al tratar de replicar los datos obtenidos por el grupo del anterior semestre, se verifico que no funcionaba el sistema, lograron operar con datos implementados en el PLC que no se replicaba en sus informes.

Los requerimientos que propusieron eran de un tiempo de establecimiento de 4 minutos, y verificamos que había saturación en el actuador (El variador de frecuencia superaba los 50Hz).

Nuestro grupo obtuvo un desempeño satisfactorio del sistema para unos 8 minutos para el tiempo de establecimiento, logrando no saturar al actuador.

# 3. DISEÑO DEL CONTROLADOR CONSIDERANDO LA DINAMICA DEL ACTUADOR

## 3.1. REQUERIMIENTOS

El diseño de un controlador por realimentación de estados, tiene los siguientes requerimientos:

- El sistema tenga un tiempo de establecimiento de 10 min
- Un máximo sobrepaso menor al 1%

## 3.2. DISEÑO DEL CONTROLADOR

Análisis del actuador VF-B


Con Matlab


Kx=9.967

k_x :dinamica del actuador

k_x =9.967

Obtención de la función de transferencia de a dinámica del actuador con el porcentaje de estimación del 92% :

4.623/(s+0.3275)


Realizamos el siguiente análisis de la representación externa:

(H(s))/(Q(s))=k_x *R/(1+RCs) k_x :dinamica del actuador

si: x_1 =h(t)

→ x_1 = h(t) → x_1 =1/C*k_x *q_i (t)-1/(RC)*x_1

De la ecuación de estados:

x(t)=Ax(t)+Bq_i (t)y(t)=Cx(t)

Obtenemos la siguiente relación:

→ A=[(-1)/(RC)], B=[(k_x)/C], C=[1]

Con: k_x =9.967

## 3.3. DISEÑO DEL CONTROLADOR EN TIEMPO CONTINUO

Trabajando con el sistema de primer orden

(H(s))/(Q_i (s))=R/(sCR+1) → (H(s))/(Q_i (s))=kx*0.09569/(303*s+1)

Tomando las ecuaciones diferenciales ordinarias que modelan el sistema (1 y 2).

x(t)=Ax(t)+Bq_i (t)y(t)=Cx(t) → A=[(-1)/303], B=[(kx)/3166.47], C=[1]

Analizamos el requerimiento (ts = 10 min = 600 seg) (con k_x =9.967 ):

600=t_s ≥4τ ; τ=600/4

Sea el polinomio característico deseado:

s+1/τ → s+6.70∙10^(-3)

La raíz que deseamos será: s=-6. 70∙10^(-3)

Calculamos las matrices de ganancia para la realimentación por el método de Ackerman:

CONSIDERANDO DINAMICA DEL ACTUADOR, UNA CONSTANTE

K=[1]*C_o^(-1) *ϕ(A)

K=[1]*[(9,96)/3166.47]^(-1) *[(-1)/303+6. 7∙10^(-3) ]

K=1*3166.5*13.367∙10^(-3)

K=1.096

## 3.4. RESULTADOS CON MATLAB


## 3.5. POLINOMIO CARACTERÍSTICO DESEADO EN ESPACIO DE ESTADOS CONTINÚO CONSIDERANDO EL ACTUADOR DE PRIMER ORDEN

Analizamos los requerimientos: 600=t_s ≥4/(ζω_n); 0.01=Mp≥e^((-ζπ)/(√(1-ζ^2))) ;

Procedimiento:

In(0.001)=(-ζπ)/(√(1-ζ^2)) → (1-ζ^2 )In(0.001)^2 =(ζπ)^2 → ζ=√((In(0.01)^2)/(In(0.01)^2 +π^2))=0.91

ω_n =4/(300*ζ) → ω_n =6.10∙10^(-3)

Sea el polinomio característico de un sistema de 2do orden:

s^2 +2ζω_n s+ω_n ^2 → s^2 +0.01s+3.663∙10^(-3)

Las raíces que deseamos serán:

s_(1,2) =-5*10^(-3) ±60.29∙10^(-3)

Donde podemos definir las siguientes ecuaciones:

(H(s))/(Q_i (s))=R/(sCR+1) *M(s) → (H(s))/(Q_i (s))=0.09569/(303*s+1)*4.623/(s+0.3275)

GP(s)=0.4424/(303*s^2 +100.2*s+0.3275)

Con las ecuaciones:

x(t)=Ax(t)+Bq_i (t)y(t)=Cx(t)

Entonces tendríamos una representación en espacio de estados de la siguiente manera:

x(t)=[-0.3307, -0.00111, 0]*x(t)+[10]u(t)

→u(t)=-K*u(t)+N*r(t)

Donde:

A=[-0.3307, -0.00111, 0], B=[10], C=[1, 0]

K=[-k1 -k2]

Verificamos la controlabilidad del sistema

Co=[B, AB] → Co=[10, -0.33071]

rango(Co)=2 ∴es controlable

Para el controlador: Calculo de la ganancia de pre compensación y de la ganancia de pre alimentación.

Sea el polinomio característico de un sistema de 2do orden:

s^2 +2ζω_n s+ω_n ^2 → s^2 +0.01s+3.663∙10^(-3)

Las raíces que deseamos serán:

s_(1,2) =-5*10^(-3) ±60.29∙10^(-3)

Por el método de Ackerman:

Donde: A=[-0.3307, -0.00111, 0], B=[10]

K=[0 1]*Co^(-1) *ϕ(A)

Para: ϕ(A)=A^2 +0.01A+3.663∙10^(-3) *I

ϕ(A)=[-0.3307, -0.00111, 0]^2 +0.01*[-0.3307, -0.00111, 0]+3.663∙10^(-3) *[1, 00, 1]

ϕ(A)=[0,1061, 01,01, 0]

Entonces: K=[0 1]*[1,010, 0,33071] *[0,1061, 01,01, 0]

K=[2,2005, 0,0002]

Utilizando Ackerman en MatLab tenemos:

K=[2,2005, 0,0002]

G(s)=C*(sI-(A-BK))^(-1) *B → G(s) ;con s=0

Si: s→0 entonces: 1/N=0.1129 → N=8,8596

Respuesta con Matlab:

## 3.6. DISEÑO DEL CONTROLADOR EN TIEMPO DISCRETO

Elección del periodo de muestreo

Entonces:

Para este caso la constante tau viene siendo el valor que acompaña a la variable “s” del denominador de la función de transferencia.

(H(s))/(Q(s))=(0,09569)/(303,030*s+1)

T=303.03/10 → T=30.30[s]

## 3.7. PLANTA DISCRETA

Criterio del tiempo de respuesta: T_s =τ/10=(303,03)/10=30.30

Y con la conversión por tablas:


La función de trasferencia en discreta será:

G(z)=(0.0006314*Z)/(Z-e^(-0,006557*T))

Y reemplazando el periodo de muestreo:

G(z)=(0.0006314*Z)/(Z-e^(-0.1987))

Simplificando:

G(z)=(0.0006314*Z)/(Z-0,8198)

## 3.8. DIAGRAMA EN DISCRETA


## 3.9. DISEÑO DE CONTROLADOR EN TIEMPO DISCRETO

Discretizando la representación interna del sistema:

x(t)=Ax(t)+Bq_i (t)y(t)=Cx(t)→ A=[(-1)/(RC)], B=[(kx)/C],

→T= A=[(-1)/303], B=[1/3166.47],

A=L^(-1) {(sI-A)^(-1) }|_T → A=e^(-3,3003∙10^(-3) T) =e^(-3,3003∙10^(-3) *30,3) =0.9048

B=B*∫_0^T {L^(-1) {(sI-A)^(-1) }dt} → B=303*(1-e^(-0.1) )B*k_x =303*(1-e^(-0.1) )*1/3166.47*9.967=91.025∙10^(-3)

C=C=1

Analizamos el requerimiento (ts = 10 min = 600 seg) con k_x =9.967 :

00/4=τ ;T=30.30 ; τ≥(-T)/(In(r)) ; r=e^(-T/τ) =0.8171

Sea el polinomio característico de un sistema deseado:

z-r → z-0.8171

Por el método de Ackerman:

K=[1]*C_o^(-1) *ϕ(A)

K=[1]*B^(-1) *[A-0.6522]

K=[1]*[91.025∙10^(-3) ]^(-1) *[0.9048 -0.0.8171 ]

K=0.9669

Calculamos la matriz de recompensación para el seguimiento a referencia:

G(z)=C*(zI-(A-BK))^(-1) *B → G(z)=(91.025∙10^(-3))/(z-0.922)

Si: z→1 entonces: 1/N=261.7159∙10^(-3) → N=2.054

# 4. CONCLUSIONES

Al considerar la dinámica del actuador los valores de la ganancia de pre compensación y pre alimentación disminuyen, lo cual nos permite implementar satisfactoriamente el controlador.

Con los nuevos requerimientos el tiempo de establecimiento de 10 minutos, se cumple tanto en simulación como en la parte experimental y teorica satisfactoriamente.

Nuestro grupo obtuvo un desempeño satisfactorio del sistema para unos 10 minutos para el tiempo de establecimiento, logrando no saturar al actuador.
