Murphyramiritus/planta-nivel-umsa---Public/historico/2023-I/BITACORA 3/Laboratorio3.pptx

## DISEÑO DEL CONTROLADOR

ETN-1034

## RESPUESTA TEMPORAL DEL SISTEMA

## Datos

Reemplazando:
Capacitancia Restricción

C=39,8 x 39,8 [cm^2 ]

C=1584[cm^2 ]

R=h/(q_s)=(25[cm])/(259.62[(cm^3)/s])

R=0.09629[s/(cm^2)]

Función de transferencia EXPERIMENTAL

(H(s))/(Q(s))=(0,09569)/(303,030∗s+1)

(H(s))/(Q(s))=R/(1+RCs)

## Slide 4

Simulando el comportamiento del sistema para un caudal de entrada de 261,1 cc/seg tenemos:


Tiempo de asentamiento:
19,83 min

## REQUERIMIENTOS

- El diseño de un controlador por realimentación de estados, tiene los siguientes requerimientos :
- El sistema tenga un tiempo de establecimiento de 4 min
- Un máximo sobrepaso menor al 1%

## DISEÑO DEL CONTROLADOR PARA UN SERVOSISTEMA


## POLINOMIO CARACTERISTICO DESEADO:

Analizamos los requerimientos:
300=t_s ≥4/(ζω_n); 0.001=Mp≥e^((−ζπ)/(√(1−ζ^2))) ;
Procedimiento:
In(0.001)=(−ζπ)/(√(1−ζ^2)) → (1−ζ^2 )In(0.001)^2 =(ζπ)^2 → ζ=√((In(0.001)^2)/(In(0.001)^2 +π^2))=0.91
ω_n =4/(300∗ζ) → ω_n =14.65∙10^(−3)
Sea el polinomio característico de un sistema de 2do orden:
s^2 +2ζω_n s+ω_n ^2 → s^2 +0.0267s+0.2146∙10^(−3)
Las raíces que deseamos serán:
s_(1,2) =−0.01335±6.0314∙10^(−3)

## Slide 8

(H(s))/(Q_i (s))=R/(sCR+1) → (H(s))/(Q_i (s))=0.09569/(303∗s+1)
Con las ecuaciones :
x(t)=Ax(t)+Bq_i (t)y(t)=Cx(t) → A=[(−1)/303], B=[1/3166.47], C=[1]

Donde podemos definir las siguientes ecuaciones:
x(t)=Ax(t)+Bu(t)y(t)=Cx(t)u(t)=k_1 ξ(t)−Kx(t)ξ(t)=r(t)−y(t)
Entonces tendríamos una representación en espacio de estados de la siguiente manera:
[x(t)ξ(t)]=[A, 0−C, 0][x(t)ξ(t)]+[B0]u(t)+[01]r(t) → x_a (t)=Ax_a (t)+Bu(t)+Er(t)u(t)=−Kx_a (t)
Donde:
A=[(−1)/(RC), 0−1, 0], B=[1/C0] y K=[K −k_1 ]
A=[−3.3003∙10^(−3) , 0−1, 0], B=[31.58∙10^(−3) 0] y K=[K −k_1 ]

## Slide 9

Verificamos la controlabilidad del sistema
Co=[B, AB] → Co=[0.625∙10^(−3) 0, −3.8989∙10^(−3) ∗0.625∙10^(−3) −0.625∙10^(−3) ]
Co=[0.625∙10^(−3) 0, −2.4368∙10^(−6) −0.625∙10^(−3) ] ∴es controlable

## Slide 10

Realizamos el siguiente análisis, partimos de la representación externa:

(H(s))/(Q(s))=R/(1+RCs)

si: x_1 =h(t)
→ x_1 = h(t)
x_1 =1/C∗q_i (t)−1/(RC)∗x_1

→ A=[(−1)/(RC)], B=[1/C], C=[1]

x(t)=Ax(t)+Bq_i (t)y(t)=Cx(t)

## DISEÑO DEL CONTROLADOR EN TIEMPO CONTINUO

Trabajando con el sistema de primer orden
(H(s))/(Q_i (s))=R/(sCR+1) → (H(s))/(Q_i (s))=0.09569/(303∗s+1)
Tomando las ecuaciones diferenciales ordinarias que modelan el sistema (1 y 2).
x(t)=Ax(t)+Bq_i (t)y(t)=Cx(t) → A=[(−1)/303], B=[1/3166.47], C=[1]
Analizamos el requerimiento (ts = 4 min = 240 seg):
240=t_s ≥4τ ; τ=60
Sea el polinomio característico de un sistema deseado:
→ s^2 +0.0267s+0.2146∙10^(−3)
→φ(A)= [(−1)/303]^2 +0.0267∗[(−1)/303]+0.2146∙10^(−3) *[1]
φ(A)=1.3737∗10^(−4)
Calculamos las matrices de ganancia para la realimentación por el método de Ackerman:
K=[1]∗C_o^(−1) ∗φ(A)
K=[1]∗[1/3166.47]^(−1) ∗[(−1)/303+16.6667∙10^(−3) ]
K=1∗3166.5∗13.367∙10^(−3)
K=42,3350
Calculamos la matriz de recompensación para el seguimiento a referencia:
G(s)=C∗(sI−(A−BK))^(−1) ∗B → G(s)=(315,80∙10^(−6))/(s+16.6667∙10^(−3))
Si: s→0 entonces: 1/N=18,9442.4999∙10^(−3) → N=52.6667

EXPERIMENTAL

Sea el polinomio característico de un sistema deseado:
s+1/τ → s+16.6667∙10^(−3)
La raíz que deseamos será:
s=−16.6667∙10^(−3)

## DISEÑO DEL CONTROLADOR EN TIEMPO CONTINUO

Trabajando con el sistema de primer orden
(H(s))/(Q_i (s))=R/(sCR+1) → (H(s))/(Q_i (s))=0.09629/(152,5∗s+1)
Tomando las ecuaciones diferenciales ordinarias que modelan el sistema (1 y 2).
x(t)=Ax(t)+Bq_i (t)y(t)=Cx(t) → A=[(−1)/(152,5)], B=[1/(1583,75)], C=[1]
Analizamos el requerimiento (ts = 4 min = 240 seg):
240=t_s ≥4τ ; τ=60
Sea el polinomio característico de un sistema deseado:
→ s^2 +0.0267s+0.2146∙10^(−3)
→φ(A)= [(−1)/303]^2 +0.0267∗[(−1)/303]+0.2146∙10^(−3) *[1]
φ(A)=1.3737∗10^(−4)
Calculamos las matrices de ganancia para la realimentación por el método de Ackerman:
K=[1]∗C_o^(−1) ∗φ(A)
K=[1]∗[1/(1583,75)]^(−1) ∗[(−1)/(152,5)+16.6667∙10^(−3) ]
K=1∗3166.5∗1.3737∗10^(−4)
K=16.02
Calculamos la matriz de recompensación para el seguimiento a referencia:
G(s)=C∗(sI−(A−BK))^(−1) ∗B → G(s)=(6.314∗10^(−4))/(s+16.6667∙10^(−3))
Si: s→0 entonces: 1/N=37.8770∙10^(−3) → N=26.4012

TEORICO

→ A=[(−1)/(RC)], B=[1/C], C=[1]

Sea el polinomio característico de un sistema deseado:
s+1/τ → s+16.6667∙10^(−3)
La raíz que deseamos será:
s=−16.6667∙10^(−3)

## Slide 13

Verificando los valores obtenidos

Una vez obtenido los valores de N=20.42 y k=26.67:
El sistema tenga un tiempo de establecimiento de 4 min
Un máximo sobrepaso menor al 1%
Si bien la simulación en matlab es buena, al introducir los valores de N y K al PLC, este manda una señal de “fault”
El sistema no funciona

## Slide 14

Verificando los valores obtenidos

Modificando el tiempo de establecimiento de 8 min
Obtenemos los valores de N=13.183 y k=2.733:
La simulación en Matlab es buena, al introducir los nuevos valores de N y K al PLC, este ya no manda una señal de “fault”
El sistema funciona.

## Slide 15


## Slide 16


## Slide 17

Programación en PLC


## Slide 18


## Slide 19


## Slide 20


## Slide 21

Conclusiones

Al tratar de replicar los datos obtenidos por el grupo del anterior semestre, se verifico que no funcionaba el sistema, lograron operar con datos implementados en el PLC que no se replicaba en sus informes.
Los requerimientos que propusieron eran de un tiempo de establecimiento de 4 minutos, y verificamos que había saturación en el actuador (El variador de frecuencia superaba los 50Hz).
Nuestro grupo obtuvo un desempeño satisfactorio del sistema para unos 8 minutos para el tiempo de establecimiento, logrando no saturar al actuador.

## DISEÑO DEL CONTROLADOR

CONSIDERANDO LA DINAMICA DEL ACTUADOR

## ANALISIS DEL ACTUADOR VF-B

FRECUENCIA | TIEMPO1 | TIEMPO2 | TPROMEDIO | CAUDAL(L/S) | VOLTAJE
20 | 27,36 | 27,21 | 27,285 | 146,600696 | 98,9
22,5 | 18,9 | 18,48 | 22,9875 | 174,007613 | 109,75
25 | 18,9 | 18,48 | 18,69 | 214,018192 | 120,6
28 | 15,27 | 15,01 | 15,14 | 264,200793 | 136,3
30 | 13,24 | 13,53 | 13,385 | 298,841987 | 145,8
33,1 | 12,01 | 11,67 | 11,84 | 337,837838 | 163,8
35 | 10,9 | 11,59 | 11,245 | 355,713651 | 173,3
37 | 9,9 | 9,7 | 9,8 | 408,163265 | 183,6
40 | 9,25 | 9,06 | 9,155 | 436,919716 | 199,9

## CON MATLAB


4.623/(s+0.3275)

k_x :dinamica del actuador
k_x =9.967

## Slide 25

Realizamos el siguiente análisis, partimos de la representación externa:

(H(s))/(Q(s))=k_x ∗R/(1+RCs)

si: x_1 =h(t)
→ x_1 = h(t)
x_1 =1/C∗k_x ∗q_i (t)−1/(RC)∗x_1

→ A=[(−1)/(RC)], B=[(k_x)/C], C=[1]

k_x :dinamica del actuador

x(t)=Ax(t)+Bq_i (t)y(t)=Cx(t)

k_x =9.967

## DISEÑO DEL CONTROLADOR EN TIEMPO CONTINUO

Trabajando con el sistema de primer orden
(H(s))/(Q_i (s))=R/(sCR+1) → (H(s))/(Q_i (s))=kx∗0.09569/(303∗s+1)
Tomando las ecuaciones diferenciales ordinarias que modelan el sistema (1 y 2).
x(t)=Ax(t)+Bq_i (t)y(t)=Cx(t) → A=[(−1)/303], B=[(kx)/3166.47], C=[1]
Analizamos el requerimiento (ts = 10 min = 600 seg):
600=t_s ≥4τ ; τ=600/4
Sea el polinomio característico deseado:
s+1/τ → s+6.70∙10^(−3)
La raíz que deseamos será: s=−6. 70∙10^(−3)
Calculamos las matrices de ganancia para la realimentación por el método de Ackerman:
K=[1]∗C_o^(−1) ∗φ(A)
K=[1]∗[(9,96)/3166.47]^(−1) ∗[(−1)/303+6. 7∙10^(−3) ]
K=1∗3166.5∗13.367∙10^(−3)
K=1.096
Calculamos la matriz de recompensación para el seguimiento a referencia:
G(s)=C∗(sI−(A−BK))^(−1) ∗B → G(s)=(3,10∙10^(−3))/(s+6. 70∙10^(−3))
Si: s→0 entonces: 1/N=0.4721 → N=2.118

EXPERIMENTAL

k_x =9.967

CONSIDERANDO DINAMICA DEL ACTUADOR ,UNA CONSTANTE

## Resultados con MATLAB


## POLINOMIO CARACTERISTICO DESEADO:

DISEÑO DEL CONTROLADOR EN TIEMPO CONTINUO

Analizamos los requerimientos:
600=t_s ≥4/(ζω_n); 0.01=Mp≥e^((−ζπ)/(√(1−ζ^2))) ;
Procedimiento:
In(0.001)=(−ζπ)/(√(1−ζ^2)) → (1−ζ^2 )In(0.001)^2 =(ζπ)^2 → ζ=√((In(0.01)^2)/(In(0.01)^2 +π^2))=0.91
ω_n =4/(300∗ζ) → ω_n =6.10∙10^(−3)
Sea el polinomio característico de un sistema de 2do orden:
s^2 +2ζω_n s+ω_n ^2 → s^2 +0.01s+3.663∙10^(−3)
Las raíces que deseamos serán:
s_(1,2) =−5∗10^(−3) ±60.29∙10^(−3)

ESPACIO DE ESTADOS EN CONTINUO CONSIDERANDO ACTUADOR DE PRIMER ORDEN

## Slide 29

Donde podemos definir las siguientes ecuaciones:
(H(s))/(Q_i (s))=R/(sCR+1) ∗M(s) → (H(s))/(Q_i (s))=0.09569/(303∗s+1)∗4.623/(s+0.3275)
GP(s)=0.4424/(303∗s^2 +100.2∗s+0.3275)
Con las ecuaciones :
x(t)=Ax(t)+Bq_i (t)y(t)=Cx(t)
Entonces tendríamos una representación en espacio de estados de la siguiente manera:
x(t)=[−0.3307, −0.00111, 0]∗x(t)+[10]u(t)
→u(t)=−K∗u(t)+N∗r(t)
Donde:
A=[−0.3307, −0.00111, 0], B=[10], C=[1, 0]
K=[−k1 −k2]

## Slide 30

Verificamos la controlabilidad del sistema
Co=[B, AB] → Co=[10, −0.33071]
rango(Co)=2 ∴es controlable

Para el controlador: Calculo de la ganancia de pre compensación y de la ganancia de pre alimentación.
Sea el polinomio característico de un sistema de 2do orden:
s^2 +2ζω_n s+ω_n ^2 → s^2 +0.01s+3.663∙10^(−3)
Las raíces que deseamos serán:
s_(1,2) =−5∗10^(−3) ±60.29∙10^(−3)

## Slide 31

Por el método de Ackerman:
Donde: A=[−0.3307, −0.00111, 0], B=[10]
K=[0 1]∗Co^(−1) ∗φ(A)
Para: φ(A)=A^2 +0.01A+3.663∙10^(−3) ∗I
φ(A)=[−0.3307, −0.00111, 0]^2 +0.01∗[−0.3307, −0.00111, 0]+3.663∙10^(−3) ∗[1, 00, 1]
φ(A)=[0,1061, 01,01, 0]
Entonces: K=[0 1]∗[1,010, 0,33071] ∗[0,1061, 01,01, 0]
K=[2,2005, 0,0002]
Utilizando Ackerman en MatLab tenemos:
K=[2,2005, 0,0002]

G(s)=C∗(sI−(A−BK))^(−1) ∗B → G(s) ;con s=0
Si: s→0 entonces: 1/N=0.1129 → N=8,8596

## Con MATLAB

## ELECCION DE PERIODO DE MUESTREO

DISEÑO DEL CONTROLADOR EN TIEMPO DISCRETO

Entonces:
Para este caso la constante tau viene siendo el valor que acompaña a la variable “s” del denominador de la función de transferencia.
T=303.03/10 → T=30.30[s]

(H(s))/(Q(s))=(0,09569)/(303,030∗s+1)

## PLANTA EN DISCRETA

- Criterio del tiempo de respuesta : T_s =τ/10=(303,03)/10=30.30


G(z)=(0.0006314∗Z)/(Z−e^(−0,006557∗T))


G(z)=(0.0006314∗Z)/(Z−e^(−0.1987))

G(z)=(0.0006314∗Z)/(Z−0,8198)

## DIAGRAMA EN DISCRETA

N

A/D

Controlador-filtro(PLC)

D/A

Planta

K

Actuador

r

f

q

h

## DISEÑO DEL CONTROLADOR EN TIEMPO DISCRETO

Discretizando la representación interna del sistema:
x(t)=Ax(t)+Bq_i (t)y(t)=Cx(t) → A=[(−1)/(RC)], B=[(kx)/C], C=[1]
A=ℒ^(−1) {(sI−A)^(−1) }|_T → A=e^(−3,3003∙10^(−3) T) =e^(−3,3003∙10^(−3) ∗30,3) =0.9048
B=B∗∫_0^T {ℒ^(−1) {(sI−A)^(−1) }dt} → B=303∗(1−e^(−0.1) )B∗k_x =303∗(1−e^(−0.1) )∗1/3166.47∗9.967=91.025∙10^(−3)
C=C=1
Analizamos el requerimiento (ts = 10 min = 600 seg):
00/4=τ ;T=30.30 ; τ≥(−T)/(In(r)) ; r=e^(−T/τ) =0.8171
Sea el polinomio característico de un sistema deseado:
z−r → z−0.8171
Por el método de Ackerman:
K=[1]∗C_o^(−1) ∗φ(A)
K=[1]∗B^(−1) ∗[A−0.6522]
K=[1]∗[91.025∙10^(−3) ]^(−1) ∗[0.9048 −0.0.8171 ]
K=0.9669
Calculamos la matriz de recompensación para el seguimiento a referencia:
G(z)=C∗(zI−(A−BK))^(−1) ∗B → G(z)=(91.025∙10^(−3))/(z−0.922)
Si: z→1 entonces: 1/N=261.7159∙10^(−3) → N=2.054

→T= A=[(−1)/303], B=[1/3166.47],

k_x =9.967

## Resultados obtenidos con MATLAB


## Slide 38

Conclusiones

Al considerar la dinámica del actuador los valores de la ganancia de precompensacion y prealimentacion disminuyen, lo cual nos permite implementar satisfactoriamente el controlador.
Con los nuevos requerimientos el tiempo de establecimiento de 10 minutos, se cumple tanto en simulación como en la parte experimental y teorica satisfactoriamente.
Nuestro grupo obtuvo un desempeño satisfactorio del sistema para unos 10 minutos para el tiempo de establecimiento, logrando no saturar al actuador.
